Sarbf1/Sensor-to-CAN/Simulation/LM234-OpAmp-LTSpice.asc

C1: cap; 100nC
I1: current; 20mA
R1: res; 1000
R2: res; 1000
R3: res; 1000
R4: res; 2000
R5: res; 1GigR
R6: res; 2000R
R7: res; 1000R
R8: res; 1000R
R9: res; 2000R
R10: res; 250R
R12: res; 1000
U1: AD8604
U2: AD8604
U3: AD8604
U4: AD8604
V1: voltage; 5
V2: voltage; 0
X1: jumper
X2: jumper
X3: jumper
X4: jumper
X5: jumper
Named nets: 0, OUT, Vin, OpAmp-in, 12V_in, 5Vin, 3V3_in
.dc V2 0 3.3 0.001
